rtitmuss/splitflap/micropython/SourceHttpd.py

import time

from Wifi import Wifi
from typing import Union, Tuple, Dict

from provider.Provider import Provider
from Display import Display
from Httpd import Httpd, decode_url_encoded
from Message import Message
from Source import Source


class SourceHttpd(Source):
    def __init__(self, wifi: Wifi, display: Display, providers: Dict[str, Provider], port: int = 0):
        self.wifi = wifi
        self.display = display
        self.providers = providers
        self.display_queue = []
        self.display_data = None
        self.scheduled_time = None

        self.default_provider = Provider()

        self.httpd = Httpd({
            "POST /display": lambda request: self.process_post_display(request),
            "GET /presets": lambda request: self.process_get_presets(request),
        }, port)

    def process_post_display(self, request: str) -> Tuple[int, bytes, str]:
        body = request.decode('utf-8').split('\r\n\r\n', 1)[1]
        form_data = decode_url_encoded(body)

        if 'text' in form_data:
            self.display_queue.append(form_data)
            return 200, b'', 'text/html'

        return 400, b'', 'text/html'

    def display_data_to_message(self, display_data: {str: str}, physical_motor_position: [int]):
        motor_position = self.display.physical_to_virtual(physical_motor_position)

        display_word = display_data['text'].upper()

        provider = self.providers.get(display_word, self.default_provider)
        message, interval_ms = provider.get_message(display_word, display_data, self.display, motor_position)

        return self.display.virtual_to_physical(message), interval_ms

    def load_message(self, is_stopped: bool, physical_motor_position: [int]) -> Union[Message, None]:
        if is_stopped:
            if self.display_queue:
                self.display_data = self.display_queue.pop(0)
                self.scheduled_time = time.ticks_ms()

            if self.scheduled_time and time.ticks_diff(self.scheduled_time, time.ticks_ms()) <= 0:
                message, interval_ms = self.display_data_to_message(self.display_data, physical_motor_position)
                self.scheduled_time = time.ticks_add(time.ticks_ms(), interval_ms) if interval_ms else None
                return message

        self.wifi.connect()
        self.httpd.poll(1000 if is_stopped else 0)
